sparkfun/SparkFun_Soft_Power_Switch_Mk2/docs/assets/3d_model/Soft_Power_Switch_JST_2mm_3D_image.png

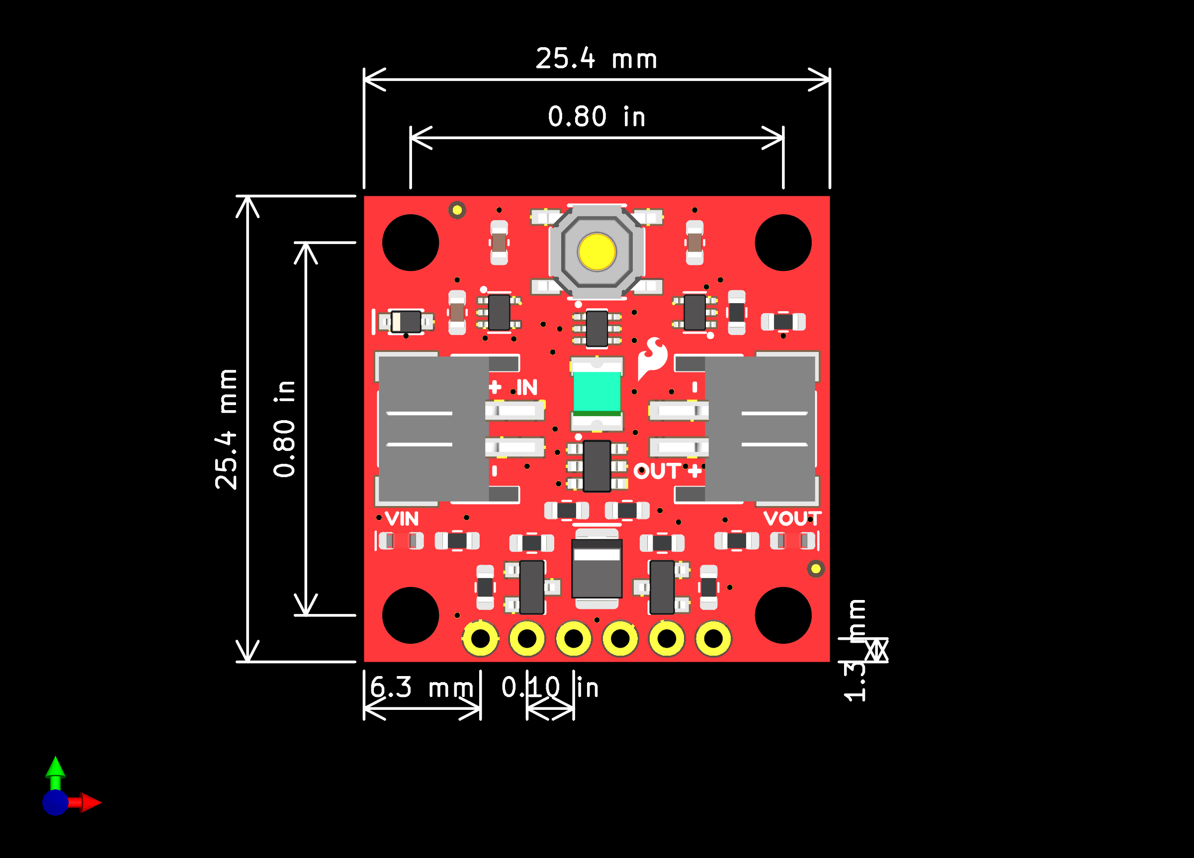
docs/assets/3d_model/Soft_Power_Switch_JST_2mm_3D_image.png
